na1pir/as3935_esp8266_iot/2015-07-26-04-01-40.png

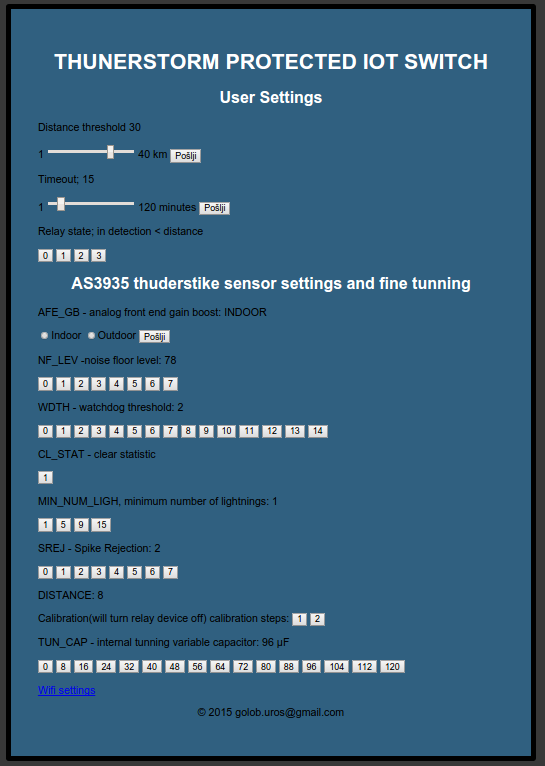
2015-07-26-04-01-40.png
