na1pir/as3935_esp8266_iot/user/driver/spi.h

/*
* The MIT License (MIT)
* 
* Copyright (c) 2015 David Ogilvy (MetalPhreak)
* 
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
* THE SOFTWARE IS PROVIDED "AS IS", WITHOUT WARRANTY OF ANY KIND, EXPRESS OR
* IMPLIED, INCLUDING BUT NOT LIMITED TO THE WARRANTIES OF MERCHANTABILITY,
* FITNESS FOR A PARTICULAR PURPOSE AND NONINFRINGEMENT. IN NO EVENT SHALL THE
* AUTHORS OR COPYRIGHT HOLDERS BE LIABLE FOR ANY CLAIM, DAMAGES OR OTHER
* LIABILITY, WHETHER IN AN ACTION OF CONTRACT, TORT OR OTHERWISE, ARISING FROM,
* OUT OF OR IN CONNECTION WITH THE SOFTWARE OR THE USE OR OTHER DEALINGS IN THE
* SOFTWARE.
*/

#ifndef SPI_APP_H
#define SPI_APP_H

#include "spi_register.h"
#include "ets_sys.h"
#include "osapi.h"
//#include "uart.h"
#include "os_type.h"

//Define SPI hardware modules
#define SPI 0
#define HSPI 1

#define SPI_CLK_USE_DIV 0
#define SPI_CLK_80MHZ_NODIV 1

#define SPI_BYTE_ORDER_HIGH_TO_LOW 1
#define SPI_BYTE_ORDER_LOW_TO_HIGH 0

#ifndef CPU_CLK_FREQ //Should already be defined in eagle_soc.h
#define CPU_CLK_FREQ 80*1000000
#endif

//Define some default SPI clock settings
#define SPI_CLK_PREDIV 7 //80/(7*1)=10  80/(3+1)=20
#define SPI_CLK_CNTDIV 9 //10/(9+1)=1   20/(9+1)=2
#define SPI_CLK_FREQ CPU_CLK_FREQ/(SPI_CLK_PREDIV*SPI_CLK_CNTDIV) // 80 / (8*10)= 1 MHz





void spi_init(uint8 spi_no);
void spi_init_gpio(uint8 spi_no, uint8 sysclk_as_spiclk);
void spi_clock(uint8 spi_no, uint16 prediv, uint8 cntdiv);
void spi_tx_byte_order(uint8 spi_no, uint8 byte_order);
void spi_rx_byte_order(uint8 spi_no, uint8 byte_order);
uint32 spi_transaction(uint8 spi_no, uint8 cmd_bits, uint16 cmd_data, uint32 addr_bits, uint32 addr_data, uint32 dout_bits, uint32 dout_data, uint32 din_bits, uint32 dummy_bits);

//Expansion Macros
#define spi_busy(spi_no) READ_PERI_REG(SPI_CMD(spi_no))&SPI_USR

#define spi_txd(spi_no, bits, data) spi_transaction(spi_no, 0, 0, 0, 0, bits, (uint32) data, 0, 0)
#define spi_tx8(spi_no, data)       spi_transaction(spi_no, 0, 0, 0, 0, 8,    (uint32) data, 0, 0)
#define spi_tx16(spi_no, data)      spi_transaction(spi_no, 0, 0, 0, 0, 16,   (uint32) data, 0, 0)
#define spi_tx32(spi_no, data)      spi_transaction(spi_no, 0, 0, 0, 0, 32,   (uint32) data, 0, 0)

#define spi_rxd(spi_no, bits) spi_transaction(spi_no, 0, 0, 0, 0, 0, 0, bits, 0)
#define spi_rx8(spi_no)       spi_transaction(spi_no, 0, 0, 0, 0, 0, 0, 8,    0)
#define spi_rx16(spi_no)      spi_transaction(spi_no, 0, 0, 0, 0, 0, 0, 16,   0)
#define spi_rx32(spi_no)      spi_transaction(spi_no, 0, 0, 0, 0, 0, 0, 32,   0)

#endif
